joelwetzel/MQTT-Locomotive/LocoPanel/include/engineOnController.h

#ifndef ENGINEONCONTROLLER_H
#define ENGINEONCONTROLLER_H

#include "locoState.h"
#include "mqttHandler.h"

#include <SparkFun_TCA9534.h>

#define ENGINE_ON_ON_BUTTON_PIN 4
#define ENGINE_ON_OFF_BUTTON_PIN 6
#define ENGINE_ON_LED_PIN 5

class EngineOnController
{
    MqttHandler &_mqttHandler;
    TCA9534 &_qwiicGpio;

    int lastOnButtonState;
    int lastOffButtonState;

public:
    EngineOnController(MqttHandler &mqttHandler, TCA9534 &qwiicGpio);

    void Setup();
    void ProcessStep(LocoState currentState);
};

#endif
