joelwetzel/MQTT-Locomotive/LocoPanel/include/locoState.h

#ifndef LOCOSTATE_H
#define LOCOSTATE_H

#include <WString.h>

struct LocoState
{
    String RoadName;
    bool MasterSwitch;
    bool EngineOn;
    int Reverser;
    float Throttle;
    int Headlights;
    bool Cablights;
    bool Bell;
    bool Horn;

public:
    LocoState()
    {
        MasterSwitch = false;
        EngineOn = false;
        Reverser = 0;
        Throttle = 0.0;
        Headlights = 0;
        Cablights = false;
        Bell = false;
        Horn = false;
    }
};

#endif
