joelwetzel/MQTT-Locomotive/LocoPanel/include/locoStateCache.h

#ifndef LOCOSTATECACHE_H
#define LOCOSTATECACHE_H

#include "locoState.h"
#include <WString.h>
#include <stdlib.h>
#include <vector>

class LocoStateCache
{
    std::vector<LocoState> cachedStates;

public:
    LocoState GetStateFor(String roadName);

    void SetMasterSwitchFor(String roadName, bool value);
    void SetEngineOnFor(String roadName, bool value);
    void SetReverserFor(String roadName, int value);
    void SetThrottleFor(String roadName, float value);
    void SetHeadlightsFor(String roadname, int value);
    void SetCablightsFor(String roadname, bool value);
    void SetBellFor(String roadname, bool value);
    void SetHornFor(String roadname, bool value);
};

#endif
