joelwetzel/MQTT-Locomotive/LocoPanel/src/engineOnController.cpp

#include "engineOnController.h"
#include <Arduino.h>

EngineOnController::EngineOnController(MqttHandler &mqttHandler, TCA9534 &qwiicGpio)
    : _mqttHandler(mqttHandler), _qwiicGpio(qwiicGpio)
{
    lastOnButtonState = 0;
    lastOffButtonState = 0;
}

void EngineOnController::Setup()
{
    _qwiicGpio.pinMode(ENGINE_ON_ON_BUTTON_PIN, GPIO_IN);
    _qwiicGpio.pinMode(ENGINE_ON_OFF_BUTTON_PIN, GPIO_IN);

    _qwiicGpio.pinMode(ENGINE_ON_LED_PIN, GPIO_OUT);
    _qwiicGpio.digitalWrite(ENGINE_ON_LED_PIN, 0);
}

void EngineOnController::ProcessStep(LocoState currentState)
{
    _qwiicGpio.digitalWrite(ENGINE_ON_LED_PIN, currentState.EngineOn);

    int currentOnButtonState = _qwiicGpio.digitalRead(ENGINE_ON_ON_BUTTON_PIN);
    int currentOffButtonState = _qwiicGpio.digitalRead(ENGINE_ON_OFF_BUTTON_PIN);

    //Serial.printf("%d\n", currentButtonState);

    if (currentOnButtonState == 0 && lastOnButtonState == 1) // Trigger on push down of the button.
    {
        // Button pushed
        _mqttHandler.SendEngineOnFor(currentState.RoadName, true);
    }
    lastOnButtonState = currentOnButtonState;

    if (currentOffButtonState == 0 && lastOffButtonState == 1) // Trigger on push down of the button.
    {
        // Button pushed
        _mqttHandler.SendEngineOnFor(currentState.RoadName, false);
    }
    lastOffButtonState = currentOffButtonState;

}
