joelwetzel/MQTT-Locomotive/LocoEngine/include/lightingDriver.h

#include <Arduino.h>

#include "config.h"
#include "iControlModel.h"
#include "batteryDriver.h"

#ifndef LIGHTINGDRIVER_H
#define LIGHTINGDRIVER_H


#ifdef ARDUINO_ESP8266_NODEMCU
    #define CAB_PIN D6
    #define FRONT_PIN D7
    #define REAR_PIN D8
#elif ARDUINO_ESP8266_WEMOS_D1MINI
    #define CAB_PIN D3
    #define FRONT_PIN D7
    #define REAR_PIN D8
#endif


enum HeadlightModes
{
    Off,
    Front,
    Rear,
    Both,
    Auto
};


class LightingDriver
{
    IControlModel* _ptrControlModel;
    BatteryDriver &_batteryDriver;


    bool _cabLightsOn;
    HeadlightModes _headlightMode;

public:
    LightingDriver(IControlModel* ptrControlModel, BatteryDriver &batteryDriver);

    void SetCabLights(bool on);
    bool GetCabLights();
    void SetHeadlights(int mode);
    HeadlightModes GetHeadlights();

    void Setup();
    void ProcessStep();
    void ChangeControlModel(IControlModel* newControlModel);
};


#endif
