joelwetzel/MQTT-Locomotive/LocoEngine/include/mqttHandler.h

#include <PubSubClient.h>
#include <ESP8266WiFi.h>
#include <ESP8266mDNS.h>
#include <ArduinoOTA.h>


#include "iControlModel.h"
#include "lightingDriver.h"
#include "soundController.h"

#include "batteryDriver.h"
#include "smokeDriver.h"
#include "tachDriver.h"
#include "pidController.h"

#include "config.h"

#ifndef MQTTHANDLER_H
#define MQTTHANDLER_H


class MqttHandler
{
    PubSubClient &_mqttClient;

    IControlModel* _ptrControlModel;
    LightingDriver &_lightingDriver;
    SoundController &_soundController;
    BatteryDriver &_batteryDriver;
    SmokeDriver &_smokeDriver;
    TachDriver &_tachDriver;
    PidController &_pidController;


    const char* ssid = WIFI_SSID; 
    const char* password = WIFI_PASSWORD;
    const char* mqtt_server = USER_MQTT_SERVER;
    const int mqtt_port = USER_MQTT_PORT;
    const char *mqtt_device_network_id = USER_DEVICE_NETWORK_ID; 

    bool boot;
    bool republish;

    int _lastControlModelId;

    bool _lastEngineOn;
    float _lastEngineRpms;
    int _lastReverser;
    int _lastHeadlights;
    bool _lastCablights;
    float _lastSmokePercent;
    float _lastWheelRpms;
    float _lastSpeedMph;

    float _lastPidControlValue;
    float _lastPidBTerm;
    float _lastPidPTerm;
    float _lastPidITerm;
    float _lastPidDTerm;

    bool _lastBell;
    bool _lastHorn;
    float _lastBattery;
    
    int _publishCounter;

    int _desiredControlModelId;

    String _masterMasterSwitchTopic;
    String _masterEngineOnTopic;
    String _masterEngineRpmsTopic;
    String _masterEnginePercentTopic;
    String _masterWheelRpmTopic;
    String _masterReverserTopic;

    void setup_wifi();
    void reconnect();
    void republishCommands();
    void publish(const char *topic, float value);
    void publish(const char *topic, int value);
    void publish(const char *topic, const char *value);

public:
    MqttHandler(PubSubClient &mqttClient, IControlModel* ptrControlModel, LightingDriver &lightingDriver, SoundController &soundController, BatteryDriver &batteryDriver, SmokeDriver &smokeDriver, TachDriver &tachDriver, PidController &pidController);

    void Setup();
    void Loop();
    void ProcessStep();
    void ChangeControlModel(IControlModel* newControlModel);

    int GetDesiredControlModelId();
};


#endif
