joelwetzel/MQTT-Locomotive/LocoSounds/include/locoTypes/alco_rs3.h

#ifndef ALCO_RS3_H
#define ALCO_RS3_H


// RS-3 specific figures
#define ENGINE_RPM_IDLE         315
#define ENGINE_RPM_1            340
#define ENGINE_RPM_2            580
#define ENGINE_RPM_MAX          1000

#endif
